mslopgk/keycab-3dprint/renders/keycap_iso.png

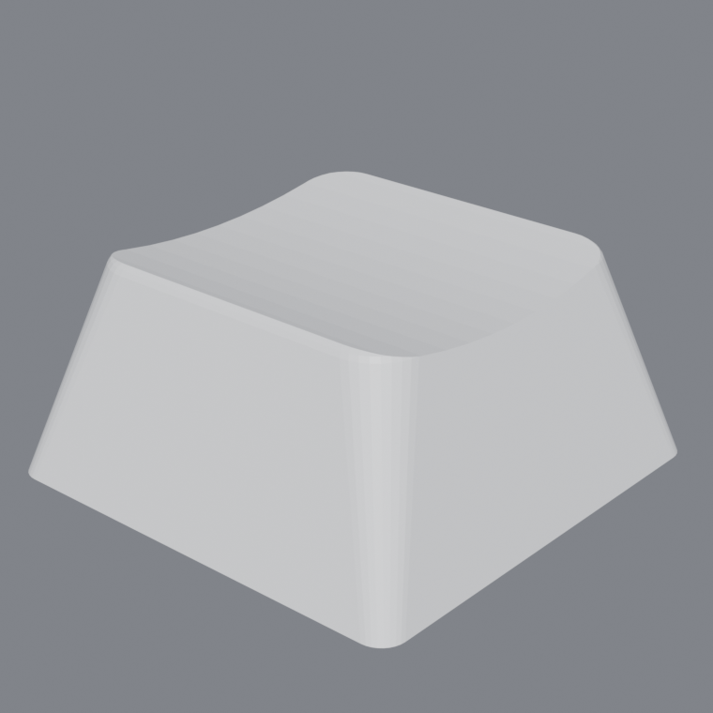
renders/keycap_iso.png
