mslopgk/keycab-3dprint/renders/keycap_underside.png

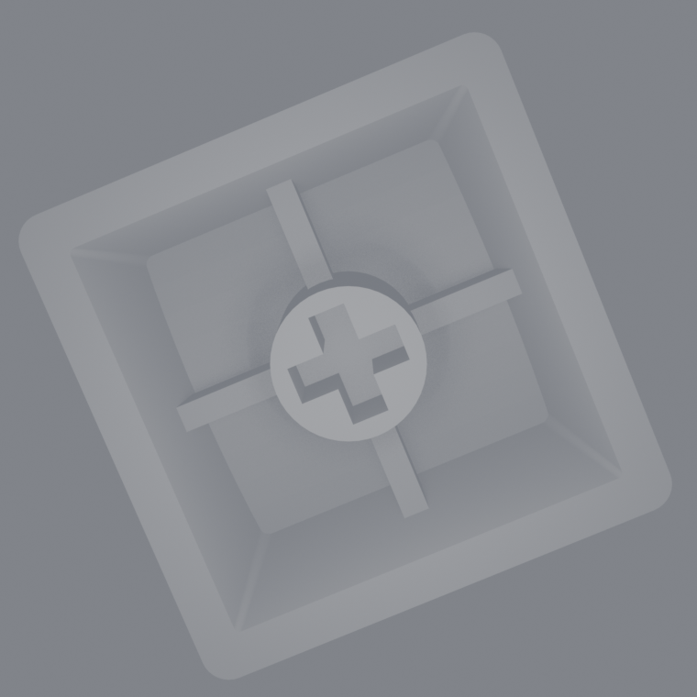
renders/keycap_underside.png
