mslopgk/keycab-3dprint/renders/keyring_iso.png

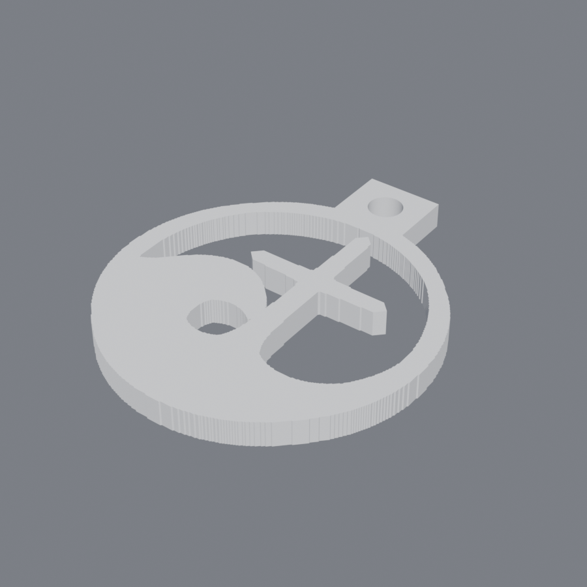
renders/keyring_iso.png
