mslopgk/keycab-3dprint/gcode/stem_gauge_220.gcode.3mf

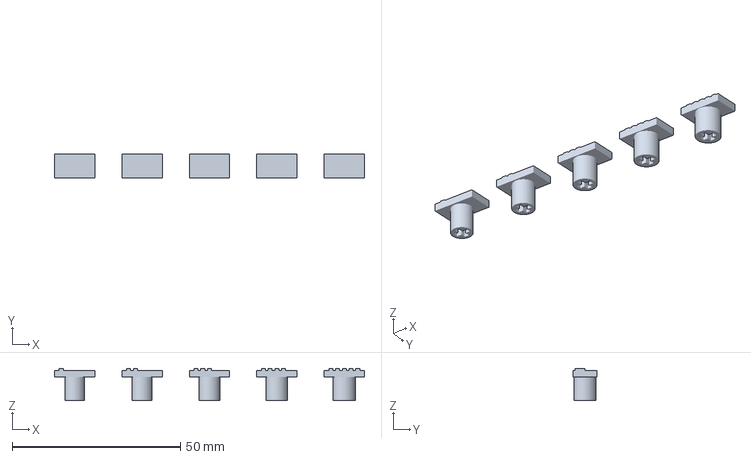
[picture p24: CAD file, 2026-09-07]
gcode/stem_gauge_220.gcode.3mf
92.0 x 7.00 x 9.60 mm
