mslopgk/keycab-3dprint/models/keycap_plate_2x2.stl

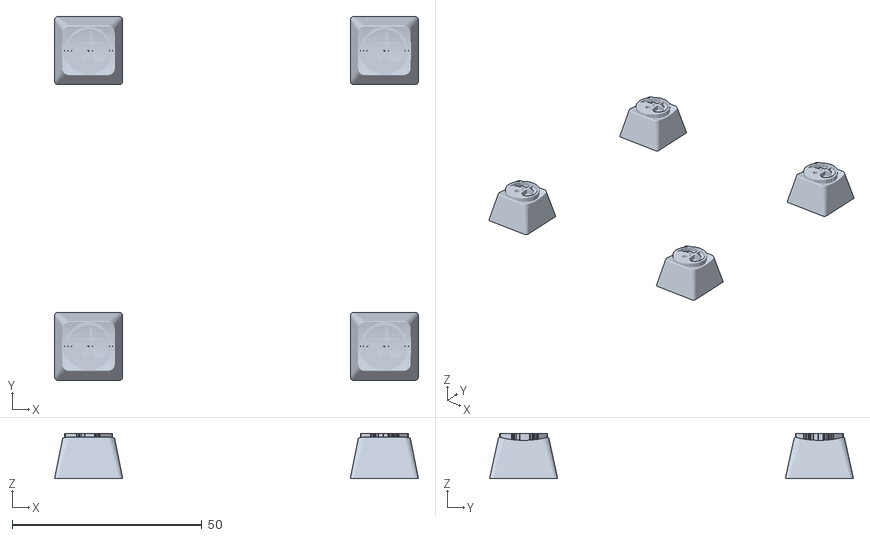
[picture p25: CAD file, 2026-09-07]
models/keycap_plate_2x2.stl
96.0 x 96.0 x 12.0
