mslopgk/keycab-3dprint/gcode/housing_fin_x9_210_028.gcode.3mf

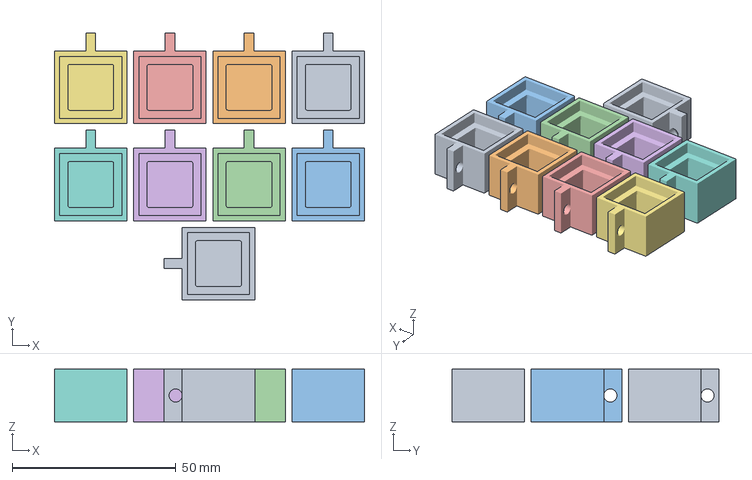
[picture p26: CAD file, 2026-09-07]
gcode/housing_fin_x9_210_028.gcode.3mf
94.8 x 81.6 x 16.2 mm
switch_housing_fin_FINAL.stl x 9
