mslopgk/keycab-3dprint/models/logo_keyring.stl

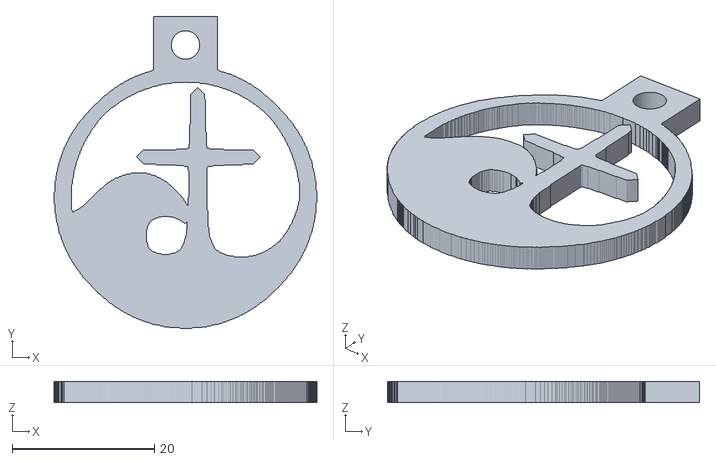
[picture p28: CAD file, 2026-09-07]
models/logo_keyring.stl
36.9 x 43.8 x 3.00
