mslopgk/keycab-3dprint/gcode/seq_probe_9.gcode.3mf

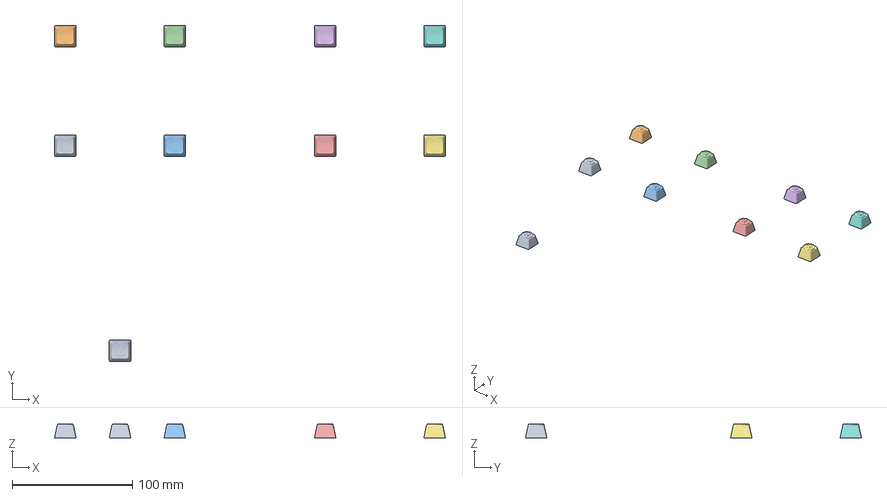
[picture p29: CAD file, 2026-09-07]
gcode/seq_probe_9.gcode.3mf
325.0 x 279.5 x 12.0 mm
keycap_1u_r3_logo_v4.stl x 9
