mslopgk/keycab-3dprint/gcode/v4_x16_seq_205_012.gcode.3mf

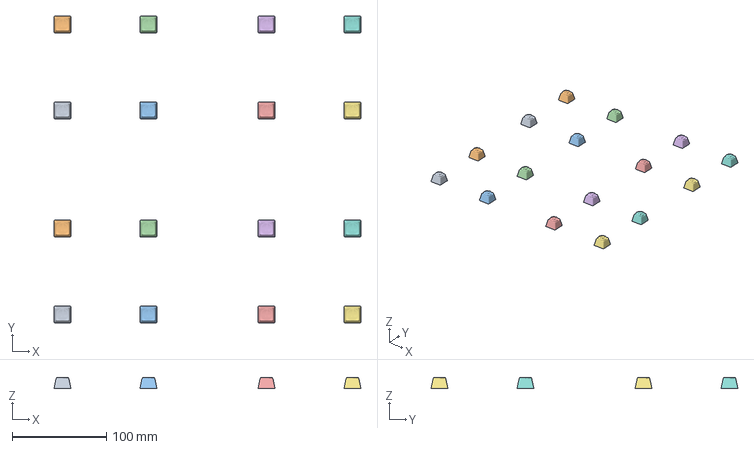
[picture p30: CAD file, 2026-09-07]
gcode/v4_x16_seq_205_012.gcode.3mf
325.0 x 325.0 x 12.0 mm
keycap_1u_r3_logo_v4.stl x 16
