mslopgk/keycab-3dprint/gcode/keychain_both.gcode.3mf

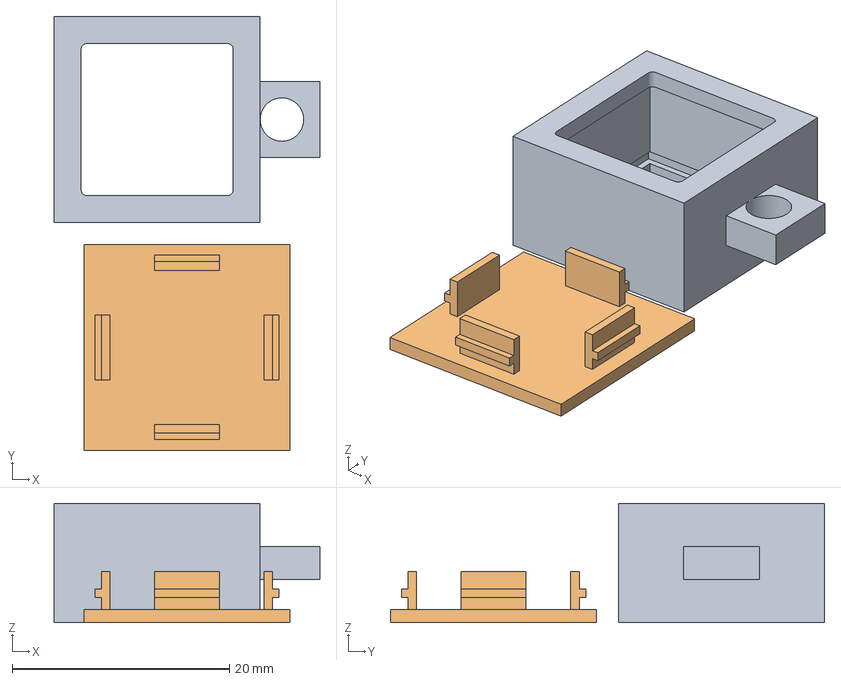
[picture p31: CAD file, 2026-09-07]
gcode/keychain_both.gcode.3mf
24.5 x 40.0 x 11.0 mm
switch_housing.stl
switch_housing_cap.stl
