mslopgk/keycab-3dprint/gcode/v3_x4_205_012_nostring.gcode.3mf

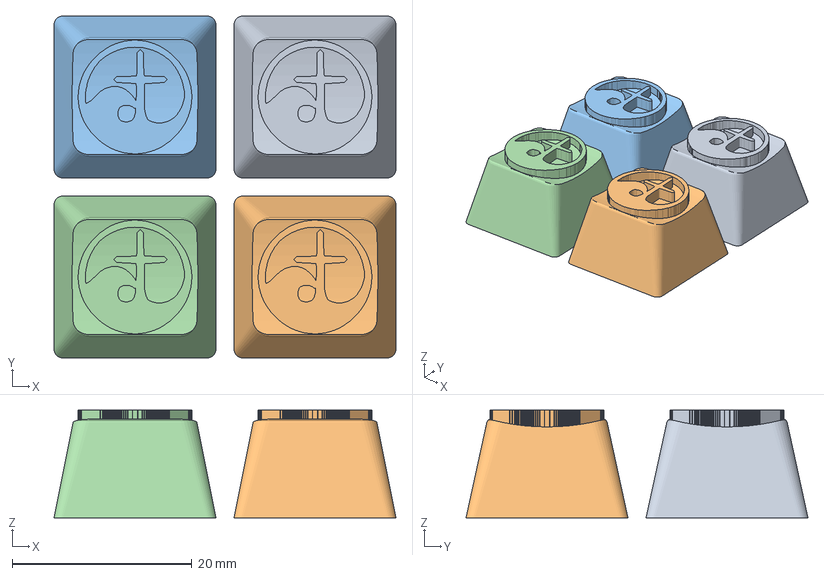
[picture p33: CAD file, 2026-09-07]
gcode/v3_x4_205_012_nostring.gcode.3mf
38.0 x 38.0 x 12.0 mm
keycap_1u_r3_logo.stl x 4
