mslopgk/keycab-3dprint/gcode/keycap_logo_x25_012.gcode.3mf

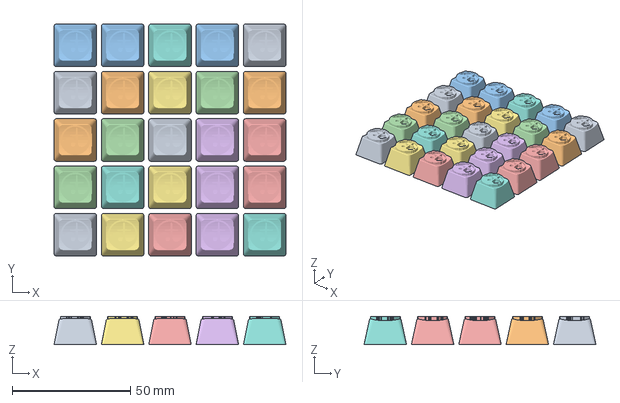
[picture p34: CAD file, 2026-09-07]
gcode/keycap_logo_x25_012.gcode.3mf
98.0 x 98.0 x 12.0 mm
keycap_1u_r3_logo.stl x 25
