mslopgk/keycab-3dprint/gcode/housing_fin_x16_210_028.gcode.3mf

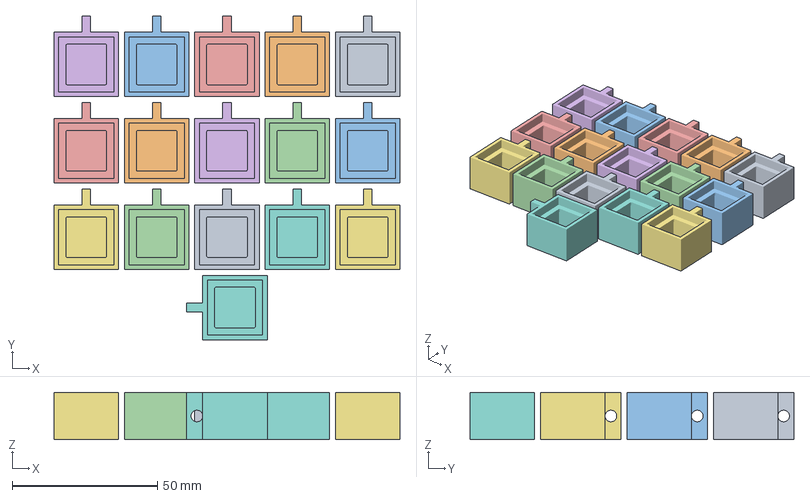
[picture p35: CAD file, 2026-09-07]
gcode/housing_fin_x16_210_028.gcode.3mf
119.0 x 111.3 x 16.2 mm
switch_housing_fin_FINAL.stl x 16
