mslopgk/keycab-3dprint/gcode/v3_x9_220_012.gcode.3mf

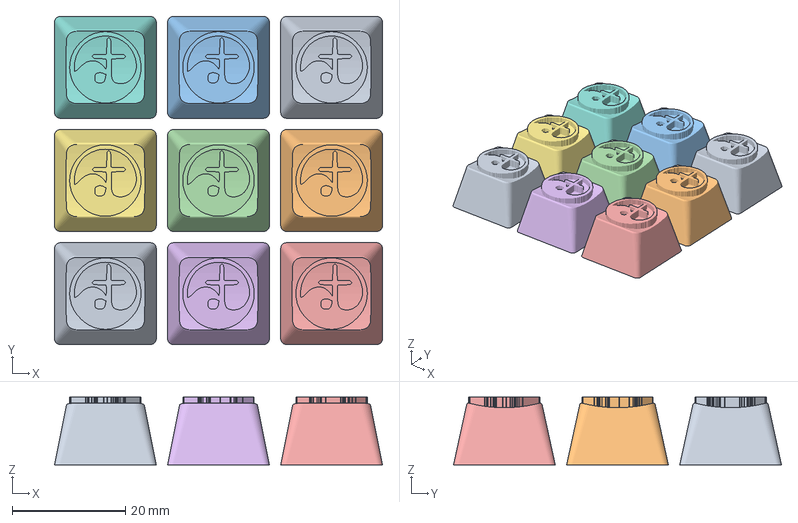
[picture p36: CAD file, 2026-09-07]
gcode/v3_x9_220_012.gcode.3mf
58.0 x 58.0 x 12.0 mm
keycap_1u_r3_logo.stl x 9
