mslopgk/keycab-3dprint/gcode/switch_housing.gcode.3mf

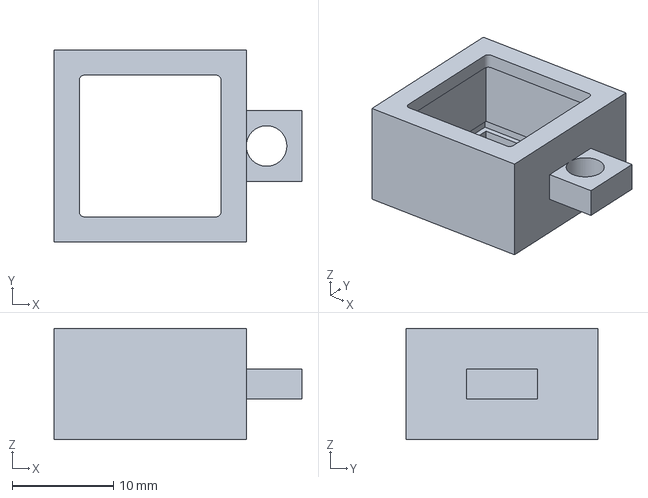
[picture p37: CAD file, 2026-09-07]
gcode/switch_housing.gcode.3mf
24.5 x 19.0 x 11.0 mm
