mslopgk/keycab-3dprint/gcode/switch_housing_cap.gcode.3mf

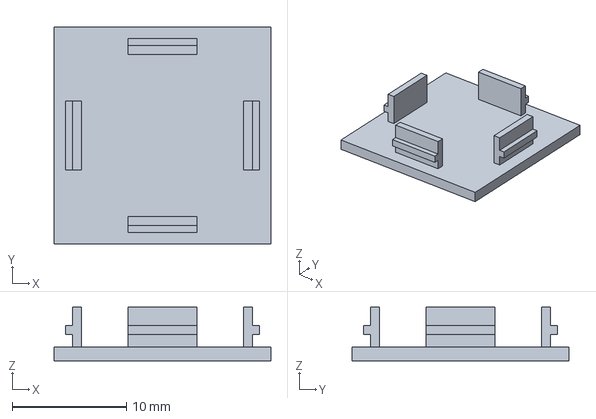
[picture p38: CAD file, 2026-09-07]
gcode/switch_housing_cap.gcode.3mf
19.0 x 19.0 x 4.70 mm
