mslopgk/keycab-3dprint/gcode/keycap_logo.gcode.3mf

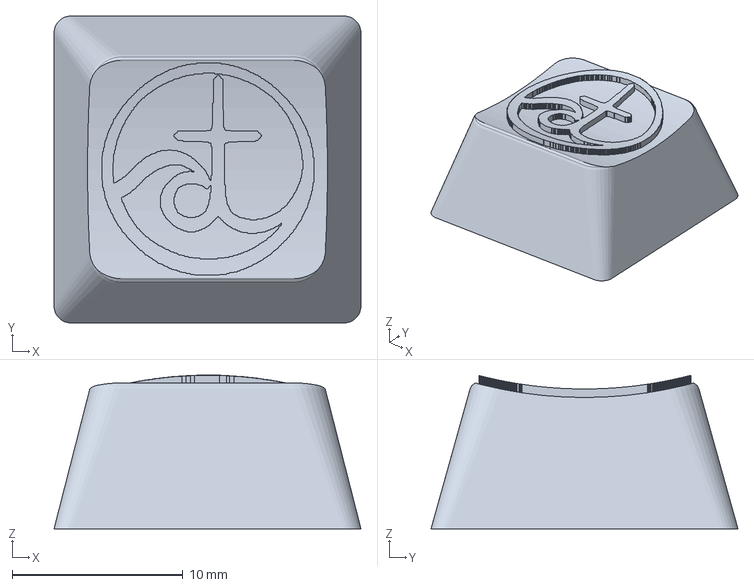
[picture p39: CAD file, 2026-09-07]
gcode/keycap_logo.gcode.3mf
18.0 x 18.0 x 9.01 mm
