mslopgk/keycab-3dprint/gcode/housing_bezel_210.gcode.3mf

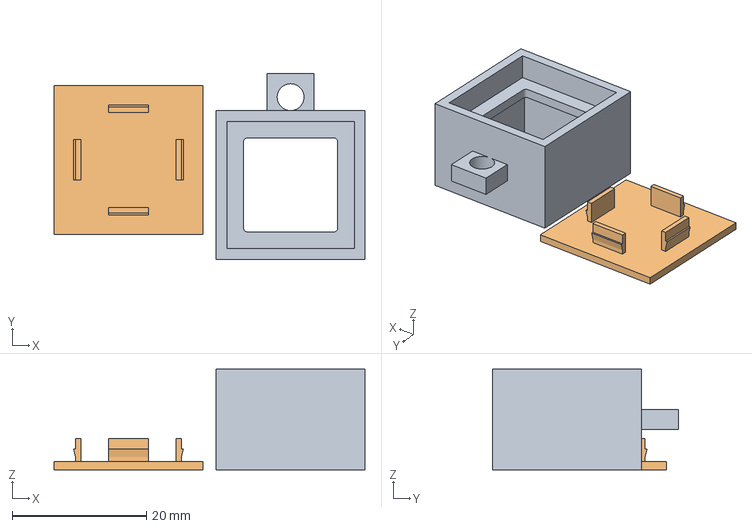
[picture p41: CAD file, 2026-09-07]
gcode/housing_bezel_210.gcode.3mf
46.4 x 27.7 x 15.0 mm
switch_housing.stl
switch_housing_cap.stl
